Lancarr8/KapTesterV2/Dokumente/Phasen/Extras/Fazit_Selbsteinschaetzung_V2.docx

Fazit und Selbsteinschätzung

KapTester V2 │ Bewertung │ AP2 2026 │ Nico Schmidt

Der folgende Abschnitt bewertet den betrieblichen Auftrag aus persönlicher Sicht: Was wurde erreicht, was lief gut, was hätte besser laufen können und was wurde dabei gelernt.

1 Zielerreichung

Das übergeordnete Ziel – einen funktionsfähigen Kapazitätstester für den Ausbildungsbetrieb zu entwickeln – ist zum Zeitpunkt der Dokumentationsabgabe weitgehend erreicht. Die Hardware-Entwicklung (Schaltplan V2, PCB V2, Bestellung) ist abgeschlossen. Die Platine wurde bestückt, gelötet und in Betrieb genommen. Die Firmware (FW3, kaptesterfw3_v11.hex) ist implementiert und läuft stabil. Ausstehend ist die abschließende Messung mit Referenzkondensatoren.

Ich bin mit dem bisherigen Stand zufrieden. Alle MUSS-Anforderungen des Lastenhefts sind im Design umgesetzt und werden durch die Inbetriebnahme- und Messtests nachgewiesen. Ob das Gerät am Ende vollständig die ±20%-Genauigkeit über den gesamten Bereich einhält, hängt noch vom Firmware-Test ab – das Messprinzip ist jedoch theoretisch und durch die Schaltungsauslegung korrekt.

2 Was gut lief

✓ Motivation und Eigeninitiative

Die Idee, etwas Eigenes zu bauen das tatsächlich im Betrieb eingesetzt werden kann, hat die Motivation über das gesamte Projekt hoch gehalten. Auch wenn die Umsetzung insgesamt mehr Zeit gekostet hat als ursprünglich gedacht, war die Bereitschaft, tiefer einzusteigen, immer vorhanden.

✓ Einstieg in KiCad und PCB-Fertigung

KiCad war zu Projektbeginn noch völlig neu. Der Weg vom ersten Symbol bis zur bestellbaren Gerber-Datei wurde komplett selbst erarbeitet. Ebenso der gesamte PCBWay-Bestellprozess mit Dimensionen, Schichtzahl, Oberflächenbehandlung und Gerber-Kontrolle. Das ist ein Werkzeug, das ich jetzt wirklich kann.

✓ SMD-Löten mit Flux

Vor dem Projekt war ich skeptisch gegenüber SMD-Bauteilen. Mit dem richtigen Flux und einer ordentlichen Lötspitze ist SMD-Löten deutlich einfacher als erwartet – und macht im Vergleich zu THT fast mehr Spaß. Das Ergebnis war optisch und elektrisch besser als gedacht.

3 Größter Fehler und was ich daraus mitgenommen habe

✗ Falsches Schaltplansymbol (DIP-28 statt TQFP-32)

Der teuerste Fehler des Projekts: Das KiCad-Symbol für den ATmega328P-AU war ein DIP-28-Simulations-Symbol ohne korrektes Pin-Mapping. Alle 32 Pins waren falsch verdrahtet. Das wurde erst nach der Bestellung und Lieferung der V1-Platine erkannt – zu spät, um zu stornieren. Die V1-Platine ist nie funktionsfähig gewesen und bleibt als Lernprototyp in der Dokumentation. Die Lektion: Symbol, Footprint und Datenblatt-Pinbelegung müssen vor jeder Bestellung konsequent gegen das Datenblatt geprüft werden – nicht nur stichprobenartig.

4 Was ich gelernt habe

Technisch:

· KiCad vollständig: Schaltplan → Footprint-Zuweisung → PCB-Layout → DRC → Gerber-Export

· PCBWay-Bestellprozess: Gerber-Viewer, Parameter (2L, 1,6mm, TG150, HASL, 1oz)

· SMD-Löten mit Flux – deutlich zugänglicher als gedacht

· LM317 als Konstantstromquelle: I = 1,25V / R – einfach, präzise, robust

· MOSFET-Schaltungen verstehen: PMOS high-side (Verpolschutz), NMOS low-side (Entladepfad)

· ADC-Timing und interne Referenz des ATmega328P

Persönlich / methodisch:

· Footprints und Symbole IMMER gegen Datenblatt prüfen, bevor bestellt wird – nicht nach dem Bestellen

· Mehr Vorab-Nachdenken spart hinten doppelte Arbeit

· Zeitschätzungen bei Hardware-Projekten deutlich großzügiger ansetzen als bei reiner Software

· Dokumentation parallel führen ist besser als alles am Ende nachzuholen

5 Was ich beim nächsten Mal anders machen würde

Footprints früher und genauer prüfen: Jedes neue Symbol sofort mit Datenblatt abgleichen – Pinbezeichnung, Gehäuseform, Pad-Anordnung. Das ist der Schritt, der mich in V1 eine komplette Platine gekostet hat.

Mehr Vorab-Nachdenken: Bevor der Schaltplan im PCB-Editor landet, würde ich mir mehr Zeit nehmen, den Stromfluss und die Schutzschaltungen auf Papier durchzudenken. R20 (Entlade-Schutzwiderstand) und die VGS-Optimierung bei Q1 hätten eigentlich schon in V1 drin sein sollen – sie kamen erst durch Review in V2.

Prototyp zuerst auf Steckbrett: Für die Kernschaltung (LM317 + ATmega + ADC) wäre ein Steckbrett-Test vor dem PCB-Design sinnvoll gewesen, um das Messprinzip real zu validieren.

6 Verbesserungspotenzial am Gerät

Das Gerät funktioniert als Prototyp. Für eine nächste Version oder einen Produktionsstand wären folgende Erweiterungen sinnvoll:

· Gehäuse: Als nackte Platine ist das Gerät anfällig für mechanische Beschädigungen und nicht ESD-geschützt. Ein einfaches 3D-gedrucktes Gehäuse würde das Gerät alltagstauglicher machen.

· Kalibrierung: Aktuell ±20 % ohne Referenznormal. Mit einem bekannten Referenzkondensator und einem Software-Kalibrierungsschritt wäre ±5 % realistisch.

· Polungsunabhängigkeit: Wenn der Kondensator verpolt angeschlossen wird, zeigt das Gerät einen Fehler. Sinnvoller wäre eine automatische Polaritätserkennung und -umschaltung, sodass die Polung des Kondensators egal ist – besonders bei schnellem Werkstatteinsatz praktisch.

· Genauere Messauflösung: Mit einem externen ADC (z.B. 16-Bit ADS1115 via I²C) wäre die Auflösung deutlich besser, besonders für kleine Kapazitäten unter 100 µF.

· ESR-Messung: Eine einfache ESR-Schätzung wäre eine wertvolle Erweiterung – schlechte Elkos haben oft erhöhten ESR lange bevor die Kapazität deutlich abnimmt.

7 Gesamteinschätzung

Das Projekt hat – trotz des Rückschlags mit der V1-Platine – insgesamt Spaß gemacht. Die Kombination aus Schaltungsentwicklung, PCB-Design, Fertigung und Inbetriebnahme ist genau das, was ich mir unter einem betrieblichen Auftrag vorstelle. Das Ergebnis ist kein perfektes Serienprodukt, aber ein funktionsfähiger, dokumentierter Prototyp der zeigt, dass ich den gesamten Weg von der Idee bis zur Inbetriebnahme selbst bestreiten kann.

Alles in allem hat es – auch wenn es manchmal nervig war – wirklich Spaß gemacht.

KapTester V2 · Fazit und Selbsteinschätzung · Nico Schmidt · IHK Osnabrück AP2 2026
