Lancarr8/KapTesterV2/Dokumente/Phasen/Extras/README_Referenz_V2.docx

Persönliche Referenz / README

KapTester V2 │ Nico Schmidt │ AP2 2026

Dieses Dokument ist meine persönliche Zusammenfassung – für die mündliche Prüfung, zum Nachschlagen und als Gedächtnisstütze. Nicht für die IHK-Abgabe bestimmt.

1 Protokoll-Phasen

Phase 0: Planungsanker – Konzept, Lastenheft, Schaltplan, BOM, Risiken

Phase 1: Fertigung – LMP ausfüllen, löten, dokumentieren, Fotos

Phase 2: Sichere Erstinbetriebnahme – spannungsfrei prüfen → kontrolliert einschalten → IBP → übergeben an MP

Phase 3: Nachweis durch Messungen – Messmittel, Messbedingungen, Messpunkte, Ergebnislogik → MP

Phase 4: Formale Abnahme / Freigabe – alle Kriterien geprüft → ANP unterschrieben

2 Schutzklassen (für die mündliche Prüfung)

SK I: Basisisolierung + Schutzleiter (PE) am berührbaren leitfähigen Gehäuse (z. B. Bohrmaschine)

SK II: Doppelte/verstärkte Isolierung, kein PE (z. B. Haartrockner)

SK III: Versorgung ausschließlich über SELV (Schutzkleinspannung, z. B. 12–24 V DC)

KapTester: NA – Baugruppe ohne Gehäuse, SELV 5 V DC → Schutzklasse abhängig von späterer Integration

3 IPC-A-610 Klassen (Lötqualität)

Klasse 1: Consumer / 'funktioniert reicht' – optische Fehler toleriert

Klasse 2: Dedicated Service / solide Industriequalität – langlebig, reproduzierbar (KapTester: Klasse 2)

Klasse 3: High-Reliability / sicherheitskritisch – Luft-/Raumfahrt, Medizintechnik

4 Messprinzip – Kapazitätsformel

Der LM317 erzeugt konstant I = 1,25 V / 1200 Ω = 1,042 mA. Der Kondensator lädt sich linear auf: U(t) = I·t/C. Umgestellt:

C = I × t / U → C = 0,001042 A × t_s / 1,1 V

Bei 100 µF: t = 100×10⁻⁶ × 1,1 / 0,001042 ≈ 0,106 s. Bei 10.000 µF: t ≈ 10,6 s. ATmega stoppt Timer wenn ADC = 1,1 V (interne Referenz).

5 AVR/Firmware – Wichtige Befehle

Fuse Bits setzen (EINMALIG – externer 16-MHz-Quarz):

avrdude -c usbasp -p m328p -U lfuse:w:0xFF:m -U hfuse:w:0xD9:m -U efuse:w:0xFF:m

Firmware flashen:

avrdude -c usbasp -p m328p -U flash:w:kaptester.hex:i

Fuse-Bits lesen (Kontrolle):

avrdude -c usbasp -p m328p -U lfuse:r:-:h -U hfuse:r:-:h

LFUSE 0xFF: Externer Quarz, volle Taktrate (CKSEL=1111, SUT=11)

HFUSE 0xD9: SPIEN=0 (ISP aktiv), EESAVE=1, Bootsize default, keine BOD-Abschaltung

I2C-Adresse: OLED SSD1306 → 0x3C

ADC-Referenz: ADMUX |= (1<<REFS1)|(1<<REFS0) → interne 1,1-V-Referenz

6 V1 → V2 Änderungen (Kerninformation für Prüfung)

Was in V1 falsch war und wie V2 es behebt:

· R6 (Risikoanalyse): ATmega DIP-28-Symbol statt TQFP-32 → alle 32 Pins falsch verdrahtet → V1 nie funktionsfähig

· R7: Kein Serienwiderstand am Q2-Drain → Einschaltstrom bei Großelkos konnte Q2 beschädigen

· Q1 Gate-Teiler: R2 war 100 kΩ → VGS = −2,5 V (suboptimal) → V2: R2 = 1 MΩ → VGS ≈ −4,5 V

· I2C: PC4/PC5 waren no-connect → V2 neu verbunden mit SDA/SCL

7 Testpunkte – Sollwerte Überblick

TP | Netz | Soll | Bedeutung
JTP1 | USB_5V | 4,80–5,20 V | Direkt von USB-VBUS
JTP2 | +5V_BOARD | 4,80–5,20 V | Nach PMOS Q1 – muss ≈ JTP1 sein
JTP4 | LM317_OUT | ≈ 4,5 V (Leerlauf) | LM317 aktiv, kein DUT
JTP5 | GND | 0 V | Massebezug
JTP6 | ADC_MEAS | 0→1,1 V während Messung | Linearer Anstieg
JTP7 | AVCC | ≈ +5V_BOARD | ADC-Versorgung
JTP8 | RESET | ≈ 5 V (Ruhe) | ATmega läuft
JTP9 | MEAS_NODE | 0→1,1 V während Messung | Wie JTP6 aber vor Filter
JTP10 | DISCH_GATE | < 0,1 V (Ruhe) / 5 V (Entladen) | Q2 gesperrt im Ruhezustand

8 Prüflingsdaten (für Abgabe)

Name: Nico Schmidt

Prüflingsnummer: (133)-1251

Ausbildungsberuf: Elektroniker für Geräte und Systeme

Ausbildungsbetrieb: GBS TEMPEST und Service GmbH, Von-Braun-Straße 8, 49356 Diepholz

Projektverantwortlicher: Andreas Moosmann · Tel. 05441 9758100/01 · a.moosmamn@gbs-tempest.de

IHK: IHK Osnabrück – Emsland – Grafschaft Bentheim, Neuer Graben 38, 49074 Osnabrück

Prüfungsdatum: 05.05.2026 (schriftliche Prüfung + Doku-Abgabe)

9 Doku-Checkliste final

✓ Deckblatt (IHK-Formular) → PDF – ausgefüllt und unterschrieben

✓ Erklärung (IHK-Formular) → PDF – ausgefüllt und unterschrieben

✓ Kopie PAO-Antrag → PDF – beigefügt

✓ Kurzbeschreibung IST/SOLL → DOCX – max. 1 Seite – fertig

✓ Dokumentenübersicht Anlagen → DOCX – Seite 2 Kurzbeschreibung – fertig

✓ Kurzbeschreibung der Phasen → DOCX – max. 5 Seiten – fertig

✓ Lastenheft V2 → DOCX – fertig

✓ Blockschaltbild → PNG/PDF – fertig

✓ Technische Schaltungsbeschreibung → DOCX – fertig

✓ Schaltplanauszug V2 (KiCad PDF) → PDF – aus KiCad exportieren

✓ Ablaufplan V2 → DOCX – fertig

✓ BOM V2 → DOCX – fertig

✓ Schnittstellentabelle V2 → DOCX – fertig

✓ Risikoanalyse V2 (R1–R7) → DOCX – fertig

✓ Löt- und Montageprotokoll V2 → DOCX – nach Löten ausfüllen

⏳ Fotos Bestückung V2 → JPG – nach Löten

⏳ Inbetriebnahmeprotokoll V2 → DOCX – nach IBN ausfüllen

⏳ Messprotokoll V2 → DOCX – nach Messung ausfüllen

⏳ Abnahmeprotokoll V2 → DOCX – nach Abnahme ausfüllen

✓ Bedienungsanleitung V2 → DOCX – fertig

✓ Fazit / Selbsteinschätzung → DOCX – nach IBN schreiben

✓ Datenblätter (Anhang) → PDF – ATmega, LM317L, IRLML6402, 2N7002

KapTester V2 · Persönliche Referenz / README · Nico Schmidt · AP2 2026
