Lancarr8/KapTesterV2/Dokumente/Phasen/Information/Lastenheft_V2.docx

Lastenheft

Kapazitätstester – KapTester V2

Dokument | Lastenheft V2.0 – Kapazitätstester | Version: V2.0 │ 26.04.2026
Autor | Nico Schmidt | IHK Osnabrück AP2 2026

1 Ausgangssituation / Problem

Bei Reparatur und Prüfung im Ausbildungsbetrieb müssen Elektrolytkondensatoren schnell auf grobe Kapazitätsabweichungen geprüft werden. Handelsübliche Multimeter sind im Bereich > 1.000 µF ungenau oder zu langsam. Außerdem besteht ein Sicherheitsrisiko durch Restladung und mögliche Verpolung beim Hantieren mit großen Kondensatoren (bis 10.000 µF). Ein dediziertes Prüfmittel ist im Betrieb nicht vorhanden.

2 Ziel des Projekts

Entwicklung eines handlötbaren Kapazitätstesters (Hybrid THT/SMD, 2-lagige Leiterplatte) zur Prüfung von Elektrolytkondensatoren im Bereich 10 µF bis 10.000 µF. Das Gerät soll Verpolschutz, automatischen Entladepfad, Start-Taster und Statusanzeige bieten. Die Messung wird optional auf einem OLED-Display (I²C) und über LEDs angezeigt.

3 Funktionsumfang (MUSS / SOLL / KANN)

Prio | Anforderung (klar, prüfbar) | Akzeptanz / Nachweis
MUSS | Messung Kapazitäten 10 µF – 10.000 µF | Messprotokoll: 5 Referenz-Kondensatoren (10, 100, 1.000, 4.700, 10.000 µF)
MUSS | Verpolung des DUT tolerieren – keine Beschädigung, Fehleranzeige | Test: DUT verpolt → rote LED, keine Erwärmung/Schaden
MUSS | DUT nach Messung automatisch entladen | Test: 4.700 µF laden → nach ≤10 s < 0,1 V (mit DMM gemessen)
MUSS | Messung startet nur nach Start-Taster-Betätigung | Funktionstest
MUSS | Fehlerzustände eindeutig über rote LED anzeigen | Testfälle: verpolt / kein DUT / Timeout
MUSS | Betriebsbereitschaft/OK über grüne LED anzeigen | Funktionstest
MUSS | Messung nach max. 15 s abbrechen und Fehler anzeigen (kein plausibles Ergebnis) | Test: offener Eingang → Timeout + Fehleranzeige
MUSS | Betrieb mit 5 V (USB) Versorgung | Test mit USB-Netzteil
SOLL | Messwert auf OLED-Display in µF anzeigen | OLED-Anzeige (SSD1306, I²C 0x3C)
SOLL | Entladezustand auf OLED anzeigen | OLED-Anzeige während Entladevorgang
KANN | Entladezeit auf OLED anzeigen | Nice-to-have, Firmwareerweiterung

4 Nicht-funktionale Anforderungen (Qualität)

· Handlötbarkeit: THT-Bedienelemente und Stecker, SMD nur TQFP-32 / SOT-23 / SOT-89 / 0805 / MELF

· Service: ISP-Header J4 (AVR-ISP-6) + Testpunkte JTP1–JTP10 für USB5V, 5VBOARD, SDA, LM317IN, GND, ADC, AVCC, RESET, MEAS, DISCH

· Messwiederholbarkeit: bei gleichem DUT drei Messungen innerhalb ±5 % (relativ)

· Sicherheit: automatischer Entladepfad mit Strombegrenzung (R20 = 470 Ω in Serie mit Q2); DUT-Klemme J3 beschriftet (+ / −)

· Layoutqualität: DRC = 0 Fehler, 0 Warnungen vor Bestellung

5 Randbedingungen (Fixpunkte)

Parameter | Festlegung
Versorgung | 5 V DC, USB Micro-B (J1, Molex 47346-0001)
Messprinzip | Konstantstromladung + ADC-Zeitmessung (ATmega328P-AU, intern 1,1-V-Referenz)
Konstantstrom | LM317L (SOT-89) + R8 (1,2 kΩ) → I = 1,25 V / 1.200 Ω = 1,042 mA
Verpolschutz | IRLML6402 PMOS (Q1), Gate-Teiler R2 = 1 MΩ / R3 = 100 kΩ → VGS ≈ −4,5 V
Entladepfad | 2N7002 NMOS (Q2) + R20 = 470 Ω (Strombegrenzer) + R9 = 100 kΩ (Gate-Pull-Down)
Mikrocontroller | ATmega328P-AU, TQFP-32, externer 16-MHz-Quarz (Y1, HC-49/U)
Display | OLED 0,96" SSD1306, I²C (J2, Adresse 0x3C), Pull-Ups R4/R5 = 4,7 kΩ
Fertigung | PCBWay, 2 Layer, FR-4 TG150, 1,6 mm, 1 oz Cu, HASL with lead
Platinenmaß | 90 × 70 mm
Umgebung | Werkstatt / Labor, ESD-Matte, Handhabung unter ESD-Schutz

6 Schnittstellen / Anschlüsse

Ref. | Typ / Footprint | Netz / Pins | Funktion | Bemerkung
J1 | USB Micro-B (Molex 47346-0001) | VBUS, GND | Versorgungseingang 5 V | D+/D− no-connect
J2 | PinHeader 1×4, P2.54 | GND, VCC, SCL, SDA | OLED-Anschluss (I²C) | SSD1306, Adresse 0x3C
J3 | Schraubklemme P5.08, 2-polig | MEAS_NODE (Pin1), GND (Pin2) | DUT-Kondensator | Polung am Silkscreen
J4 | AVR-ISP-6 (2×3, P2.54) | MOSI/MISO/SCK/RESET/VCC/GND | ISP-Programmierung | USBasp, Pin1 markiert
JTP1–10 | PinHeader 1×1, P2.54 | USB5V, 5VBOARD, SDA, LM317IN, GND, ADC, AVCC, RESET, MEAS, DISCH | Testpunkte Inbetriebnahme | Alle wichtigen Netze zugänglich

7 Abnahmekriterien (Definition 'fertig')

Nr. | Testfall | Soll (±20 %) | Ist | OK?
1 | Messung 100 µF Referenzkondensator | 80 µF – 120 µF
2 | Messung 1.000 µF Referenzkondensator | 800 µF – 1.200 µF
3 | Messung 4.700 µF Referenzkondensator | 3.760 µF – 5.640 µF
4 | Messung 10.000 µF Referenzkondensator | 8.000 µF – 12.000 µF
5 | Verpolschutz-Test (DUT verpolt) | Fehleranzeige, kein Schaden, kein Strom
6 | Entladung 4.700 µF nach Messung | < 0,1 V in ≤ 10 s (DMM gemessen)
7 | Kein DUT angeschlossen | Timeout ≤ 15 s, rote LED, OLED Fehlermeldung
8 | Messwiederholbarkeit (3× gleicher DUT) | 3 Messungen innerhalb ±5 % relativ

Messprinzip: Konstantstromladung ohne kalibriertes Referenznormal. Toleranz ±20 % resultiert aus Bauteilstreuung (R8: ±1 %) und interner 1,1-V-Referenz des ATmega (±10 % lt. Datenblatt).

8 Abgrenzung / Nicht-Ziele

· Keine ESR-Messung (Equivalent Series Resistance) · Keine Leckstrommessung als eigener Messwert

· Kein Gehäuse – Prototyp als nackte Leiterplatte · Keine Kalibrierung mit externem Referenznormal

KapTester V2 · Lastenheft V2.0 · Nico Schmidt · IHK Osnabrück AP2 2026
