Lancarr8/KapTesterV2/Dokumente/Phasen/Information/Technische_Schaltungsbeschreibung_V2.docx

Technische Schaltungsbeschreibung

KapTester V2 │ Nico Schmidt │ IHK Osnabrück AP2 2026

Diese Beschreibung erläutert alle Funktionsblöcke der V2-Platine in der Reihenfolge des Signalpfads von der Stromversorgung bis zur Messwertausgabe. Alle Bauteil-Bezeichnungen beziehen sich auf den aktuellen Schaltplan V2 (KiCad).

1. Stromversorgung – J1 – USB Micro-B

Sobald ein USB-Kabel eingesteckt wird, liegen an VBUS 5 V an. Der USB-Standard liefert bis zu 500 mA – für diese Schaltung mit maximal ~50 mA mehr als ausreichend. Die D+/D−-Datenleitungen sind bewusst nicht angeschlossen (no-connect), da nur die Versorgung benötigt wird.

2. Verpolschutz – Q1 (IRLML6402, PMOS) + R2 (1 MΩ) + R3 (100 kΩ)

Die 5 V von USB gelangen zuerst durch Q1, einen P-Kanal-MOSFET. R2 (1 MΩ, nach +USB_5V) und R3 (100 kΩ, nach GND) bilden einen Spannungsteiler: V_Gate ≈ 0,45 V, damit VGS ≈ −4,55 V. Das schaltet Q1 sicher und vollständig durch. Erst nach Q1 entsteht das interne Netz +5V_BOARD, das alle weiteren Stufen speist. Bei Verpolung oder Überspannung bleibt Q1 gesperrt und schützt die gesamte Schaltung.

Hinweis V2: V2-Änderung: R2 wurde von 100 kΩ auf 1 MΩ geändert. Damit liegt VGS bei ca. −4,5 V statt −2,5 V → robusteres Einschalten des PMOS.

3. Statusanzeige – D1 (LED grün, LED_PWR) + R6 (330 Ω) · D2 (LED rot, LED_ERR) + R7 (330 Ω)

Sobald +5V_BOARD anliegt, kann D1 (grüne LED) leuchten. R6 begrenzt den Strom: (5 V − 2 V) / 330 Ω ≈ 9 mA – gut sichtbar, nicht überlastet. D2 (rote LED) mit R7 ist identisch aufgebaut, wird jedoch vom ATmega aktiv gesteuert, z. B. bei Timeout oder Überbereich.

4. Start-Taster – SW1 + R10 (10 kΩ Pull-Up)

R10 hält den Pin START_BTN (ATmega PC2) im Ruhezustand über +5V_BOARD auf High-Pegel. Beim Drücken von SW1 wird der Pin auf GND gezogen → Low-Pegel → ATmega startet die Messung. C8 (10 nF) parallel zu SW1 wirkt als Entprellkondensator.

5. Konstantstromquelle – U2 (LM317L, SOT-89) + R8 (1,2 kΩ)

Der LM317 ist das Herzstück der Messtechnik. Zwischen VO (Ausgang) und ADJ (Stelleingang) liegt R8 (1,2 kΩ). Der LM317 hält intern immer genau 1,25 V über R8, unabhängig von der Last. Daraus ergibt sich ein konstanter Strom: I = 1,25 V / 1.200 Ω = 1,042 mA. Dieser Strom fließt durch den angeschlossenen Kondensator und lädt ihn linear auf.

6. DUT-Anschluss – J3 (Schraubklemme, 2-polig)

An J3 wird der zu messende Kondensator angeschlossen: Pin 1 = MEAS_NODE (Plus), Pin 2 = GND (Minus). Der 1,042-mA-Konstantstrom aus dem LM317 fließt in den Kondensator und lädt ihn linear auf. Der entscheidende Vorteil gegenüber der RC-Methode: Bei konstantem Strom steigt die Spannung am Kondensator exakt linear mit der Zeit an.

7. Messprinzip und ADC-Formel – U1 (ATmega328P-AU, ADC0/PC0)

Während der Kondensator lädt, steigt MEAS_NODE linear: U(t) = (I × t) / C. Umgestellt: C = I × t / U. Der ATmega misst die Zeit t (mit einem 16-Bit-Timer) bis die Spannung U die interne 1,1-V-Referenz erreicht. Da die interne Referenz stabiler als AVCC ist, ist die Schwelle präzise definiert. Bei 100 µF: t = 100×10⁻⁶ × 1,1 / 0,001042 ≈ 0,106 s – gut messbar.

8. ADC-Eingangsfilter – R1 (1 kΩ) + C8 (10 nF)

R1 (1 kΩ) bildet einen Schutzwiderstand vor dem ADC-Eingang (ESD-Schutz, PC0/ADC0). Ein zusätzlicher Filterkondensator ist nicht bestückt.

9. Mikrocontroller – U1 (ATmega328P-AU, TQFP-32)

Der ATmega ist das Steuergehirn: Er liest SW1 (PC2), steuert D1/D2 (PD2, PD3), gibt das Entladesignal aus (PB1 → DISCH_GATE), misst die Spannung (PC0 = ADC0) und berechnet die Kapazität. Wichtige Konfiguration in der Firmware: ADC-Referenz = interne 1,1 V (ADMUX |= (1<<REFS1)|(1<<REFS0)), Timer im CTC-Modus, ADC-Prescaler = 128 (125 kHz bei 16 MHz).

10. Taktgenerator – Y1 (16 MHz Quarz, HC-49/U) + C6/C7 (22 pF)

Der Quarz Y1 schwingt bei exakt 16 MHz. C6 und C7 (je 22 pF, direkt gegen GND) bilden den Lastkreis. Im PCB-Layout sitzen alle drei Bauteile direkt neben den XTAL-Pins mit kürzest möglichen Leiterbahnen. Die ATmega-Fuse-Bits müssen auf externen Quarz gesetzt sein (LFUSE = 0xFF).

11. Entladepfad – Q2 (2N7002, NMOS) + R20 (470 Ω) + R9 (100 kΩ Gate-Pull-Down)

Nach jeder Messung muss der Kondensator entladen werden. Der ATmega zieht DISCH_GATE (PB1) auf High → Q2 öffnet → Kondensator entlädt sich über R20 und Q2 nach GND. R20 (470 Ω) begrenzt den Einschaltstrom bei großen geladenen Elkos und schützt Q2. R9 (100 kΩ) hält das Gate von Q2 im Ruhezustand sicher auf Low, sodass Q2 auch bei tristatetem ATmega-Pin nicht ungewollt leitet.

Hinweis V2: V2-Änderung: R20 (470 Ω) neu hinzugefügt als Schutzwiderstand in Serie mit Q2-Drain. In V1 fehlte dieser – bei großen Elkos hätte der Entladeimpuls Q2 beschädigen können.

12. Abblockkondensatoren – C1/C2/C5 (je 100 nF, VCC) · C3 (100 nF, VCC) · C4 (100 nF, AVCC)

Fünf Keramikkondensatoren direkt an den Versorgungspins des ATmega unterdrücken Stromspitzen beim Schalten digitaler Ausgänge. C4 (AVCC) ist besonders kritisch: Störungen auf der Analog-Versorgung würden den ADC-Messwert direkt verfälschen.

13. ISP-Programmierschnittstelle – J4 (AVR-ISP-6, 2×3-Header, 2,54 mm)

Über J4 wird die Firmware mit einem USBasp-Programmer (10-Pin→6-Pin-Adapter) in den ATmega geladen. Die sechs Pins: MOSI (Daten rein), MISO (Daten raus), SCK (Takt), RESET (Programmierstart), VCC (+5V), GND.

14. OLED-Anzeige – J2 (4-Pin-Header, 2,54 mm) · R4/R5 (je 4,7 kΩ, I²C Pull-Up)

J2 führt die I²C-Leitungen SDA (PC4) und SCL (PC5) des ATmega heraus. R4 und R5 sind die I²C-Bus-Pull-Up-Widerstände nach +5V_BOARD. Ein SSD1306-OLED (0,96", I²C-Adresse 0x3C) zeigt den gemessenen Kapazitätswert an. Pinbelegung J2: Pin 1 = GND, Pin 2 = VCC, Pin 3 = SCL, Pin 4 = SDA.

Messpfad – Zusammenfassung

USB → Q1 (Verpolschutz) → +5V_BOARD → U2/LM317 (1,042 mA) → J3/DUT-Kondensator lädt linear → ATmega misst Zeit bis 1,1 V am ADC → C = I × t / U → OLED zeigt Ergebnis → Q2 + R20 entladen Kondensator

KapTester V2 · Nico Schmidt · IHK Osnabrück · AP2 2026
