Lancarr8/KapTesterV2/Dokumente/Phasen/Planung/Ablaufplan_V2.docx

Ablaufplan V2

KapTester V2 │ Planung │ AP2 2026

Schritte 1–14: Entwicklung und Fertigung V1/V2. Schritte 15–21: Inbetriebnahme, Test und Abschluss.

Nr. | Schritt | Details / Tätigkeiten | Status | Datum

INFORMATION & PLANUNG
1 | Lastenheft erstellen | · Messbereich & Genauigkeitsziel festlegen · Messmethode definieren · Bedienkonzept, Anschlüsse, Randbedingungen | ✅ Erledigt | März 26
2 | Blockdiagramm + Schnittstellentabelle | · Module definieren (ATmega, OLED, Taster, LEDs, LM317, PMOS, Entladepfad) · Netznamen festlegen (ADC_MEAS, MEAS_NODE, DISCH_GATE …) · Signalpfade dokumentieren | ✅ Erledigt | März 26
3 | Risikoanalyse erstellen | · ADC-Rauschen, Quarzstart, Verpolung, Großelko-Entladung analysieren · Gegenmaßnahmen im Layout und Schaltplan definieren | ✅ Erledigt | März 26
4 | Bauteilauswahl / BOM freeze | · THT/SMD-Mix festlegen · Footprints fixieren (Schraubklemme P5.08, Taster H5mm, LED 5mm) · Bestellung planen | ✅ Erledigt | März 26

SCHALTPLAN & PCB V1
5 | Schaltplan V1 fertigungsreif | · Netlabels vollständig · Testpunkte definiert · Pull-Ups, Filter, Vorwiderstände final · ERC = 0 Fehler | ✅ Erledigt | Apr 26
6 | PCB-Planung (Mechanik + Platzierung) | · Boardgröße 80×60 mm (V1) · Platzierungsstrategie: Digital/Analog/Power · Stecker und Bedienelemente an Rand | ✅ Erledigt | Apr 26
7 | KiCad: Schaltplan + Footprints + Annotieren | · Symbol ATmega: FALSCH – DIP-28 statt TQFP-32 verwendet (V1-Fehler, R6) · Footprints zugewiesen, ERC grob geprüft | ✅ Erledigt | Apr 26
8 | KiCad PCB: Board Outline | · Edge.Cuts, Netclasses,· DRC = 0 Fehler (V1) | ✅ Erledigt | Apr 26
9 | Bauteilplatzierung V1 | · Mechanik/Stecker am Rand, MCU zentral · Quarz direkt an XTAL-Pins · ADC-Filter nahe ADC-Pin | ✅ Erledigt | Apr 26
10 | Routing V1 | · XTAL, ADC_MEAS,· GND-Fläche Bottom | ✅ Erledigt | Apr 26
11 | Copper Pour / GND-Stitching | · Bottom GND-Fläche · GND-Vias an MCU, ADC-Filter, Power-Block | ✅ Erledigt | Apr 26
12 | DRC + Fertigungscheck V1 | · DRC = 0 kritische Fehler · Silkscreen ok, Polarity-Marken ok | ✅ Erledigt | Apr 26
13 | Gerber/Drill exportieren V1 | · Alle Layer, PTH+NPTH-Bohrungen · Gerber-Viewer geprüft | ✅ Erledigt | Apr 26
14 | PCBWay Bestellung V1 | · ZIP hochladen, Preview geprüft · V1 bestellt (DIP-28-Fehler entdeckt nach Bestellung) | ✅ Erledigt | Apr 26

SCHALTPLAN & PCB V2 (Fehlerkorrektur)
V2 | V2 Schaltplan + PCB neu erstellt | · ATmega328P-AU TQFP-32 Symbol korrekt (R6 behoben) · PC4/PC5 mit I²C SDA/SCL verbunden · R2 = 1 MΩ (Gate-Teiler Q1, VGS ≈ −4,5 V) · R20 = 470 Ω neu (Entlade-Schutzwiderstand Q2-Drain) · DRC = 0 Fehler · Gerber exportiert · PCBWay V2 bestellt: 90×70 mm, 5 Stück | ✅ Erledigt | 23.05.26

INBETRIEBNAHME & TEST
15 | Bauteile und Platinen V2 annehmen | · Platinen auf Schäden prüfen, Outline messen · Bauteile gegen BOM abgleichen · Fehlende Teile: R4/R5/R20/OLED bestellen | ✅ Erledigt | 23.05.26
16 | Platine V2 bestücken und löten | · Reihenfolge: SMD-Passivteile → SMD-ICs → TQFP-32 → THT → Quarz → USB → Header → Klemme → LEDs/Taster · Lötprotokoll parallel ausfüllen · Fotos: leer / nach SMD / nach THT / Gesamtansicht | ✅ Erledigt | 23.05.26
17 | Abweichungen dokumentieren | · Auffälligkeiten im Lötprotokoll festhalten · Risikoanalyse bei Bedarf aktualisieren | ✅ Erledigt | 23.05.26
18 | Inbetriebnahme V2 | · Kurzschlusscheck (Ohmmeter GND↔+5V) · Ersteinschalten 5 V / 100 mA Strombegrenzung · Spannung JTP1–JTP10 messen · Grüne LED muss leuchten · Inbetriebnahmeprotokoll ausfüllen | ✅ Erledigt | 23.05.26
19 | Firmware flashen (ATmega328P-AU) | · USBasp via J4 (AVR-ISP-6) · Fuse Bits: lfuse 0xFF / hfuse 0xD9 / efuse 0xFF · Firmware kaptester.hex laden · OLED-Anzeige prüfen | ✅ Erledigt | 23.05.26
20 | Funktionsprüfung + Messprotokoll | · 5 Referenz-Kondensatoren: 10 / 100 / 1.000 / 4.700 / 10.000 µF · Verpoltest · Entladetest · Timeout-Test · Ergebnisse in Messprotokoll eintragen | ✅ Erledigt | 23.05.26
21 | Abnahme + Dokumentationsabschluss | · Abnahmeprotokoll ausfüllen · Alle Anlagen zusammenstellen · Fazit / Selbsteinschätzung schreiben · IHK-Deckblatt + Erklärung beifügen | ✅ Erledigt | 23.05.26

KapTester V2 · Ablaufplan V2 · Nico Schmidt · IHK Osnabrück AP2 2026
