Lancarr8/KapTesterV2/Dokumente/Phasen/Planung/Risikoanalyse_V2.docx

Risikoanalyse V2

KapTester V2 │ Planung │ AP2 2026

Identifizierte Risiken, Ursachen, Auswirkungen und umgesetzte Gegenmaßnahmen. Stand V2 (26.04.2026).

ID | Risiko / Status
R1 | ADC-Rauschen / Messwertinstabilität [Im Design berücksichtigt]
| Ursache: Digitale Schaltvorgänge (I²C, ISP, LEDs), Stromsprünge im Lade-/Entladepfad. Auswirkung: Kapazitätswert schwankt, Fehlmessung, Fehltrigger an ADC-Schwelle. Maßnahmen: Zonentrennung Digital/Analog/Power. R1 (1 kΩ) als ESD-Schutz direkt am ADC-Pin . GND-Fläche Bottom + Via-Stitching. ADC_MEAS-Leitung kurz, fern von SCK/SCL. Nachweis: Dreifachmessung gleicher DUT: Streuung ≤ ±5 % (relativ). Gemessen im Messprotokoll.
R2 | Quarz startet nicht / instabiler Takt [Im Design berücksichtigt]
| Ursache: Lange XTAL-Leitungen, Störkopplung durch digitale Signale, schlechter GND-Rückweg Cs. Auswirkung: ATmega startet nicht, sporadische Resets, falsches Timing (Messfehler). Maßnahmen: Y1 + C6/C7 so nah wie möglich an XTAL1/XTAL2 platziert. Kurze, symmetrische XTAL-Leitungen. Saubere GND-Anbindung der Lastkondensatoren. Nachweis: MCU startet reproduzierbar nach Power-On. Firmware läuft stabil.
R3 | Verpolung / Fehlbedienung am DUT-Anschluss [Im Design berücksichtigt]
| Ursache: Elko falsch herum angeschlossen, Klemme verwechselt, Restladung am DUT. Auswirkung: Bauteilschaden (DUT/Schaltung), Fehlmessungen, Sicherheitsrisiko (Erwärmung). Maßnahmen: PMOS Verpolschutz Q1. Eindeutige Silkscreen-Beschriftung DUT+/DUT−. Firmware sperrt Messung bei Unplausibilität und zeigt LED_ERR. Nachweis: Verpolt anschließen: keine Beschädigung, keine Erwärmung, Fehleranzeige aktiv.
R4 | Große Elkos: hohe Energie / Entladung zu langsam / thermische Belastung
| Ursache: Kapazitäten bis 10.000 µF, hohe gespeicherte Energie, zu kleiner Entladepfad. Auswirkung: Lange Wartezeiten, gefährliche Restladung, Bauteilbelastung an Q2. Maßnahmen: Q2 (2N7002) + R20 (470 Ω, V2-neu) als strombegrenzter Entladepfad. R9 = 100 kΩ als Gate-Pull-Down. Firmware überwacht Entladezeit mit Timeout. Nachweis: 4.700 µF nach Messung < 0,1 V in ≤ 10 s. Mit DMM gemessen (Messprotokoll).
R5 | USB-Versorgung instabil / Spannungseinbruch bei Lastwechsel [Im Design berücksichtigt]
| Ursache: Schwaches USB-Netzteil, Stromspitzen beim Laden/Entladen, dünne 5V-Leiterbahn. Auswirkung: Reset, Fehlmessung, sporadisches Verhalten des ATmega. Maßnahmen: 5V-Leiterbahn breiter geroutet. Abblockkondensatoren C1–C5 nahe MCU-Versorgungspins. Betrieb nur an USB-Netzteilen ≥ 500 mA empfohlen. Nachweis: Betrieb an Laptop-USB und Handy-Netzteil stabil über Testdauer.
R6 | Falsches Schaltplansymbol ATmega V1 (DIP-28 statt TQFP-32) [Behoben]
| Ursache: ATmega328-P (DIP-28 Simulation) statt ATmega328P-AU (TQFP-32) im KiCad-Schaltplan verwendet. Alle Pins inkompatibel. Auswirkung: Alle Versorgungspins, XTAL und Signale falsch verdrahtet. V1-Platine nie funktional. Maßnahmen: Symbol in V2 durch ATmega328P-AU (TQFP-32, 32 Pins) ersetzt. Alles neu. Nachweis: V2-Schaltplan per Datenblatt verifiziert. PCB DRC = 0 Fehler. V2 bestellt.
R7 | Fehlender Entladewiderstand Q2 in V1 (Einschaltstrom-Risiko) [Behoben]
| Ursache: In V1 war kein Serienwiderstand am Drain von Q2. Bei vollem 10.000-µF-Elko: fließen kurzzeitig mehrere Ampere durch Q2 Auswirkung: Thermische Überlastung / Zerstörung Q2 bei großen Kondensatoren. Maßnahmen: R20 = 470 Ω neu in V2 in Serie mit Q2-Drain eingefügt. Spannungsabfall während Messung: 470 Ω × 1,042 mA = 0,49 mV – vernachlässigbar. Nachweis: Entladetest 4.700 µF: Q2 bleibt kalt, Entladezeit < 10 s.

KapTester V2 · Risikoanalyse V2 · Nico Schmidt · IHK Osnabrück AP2 2026
