Lancarr8/KapTesterV2/Dokumente/Phasen/Planung/Schnittstellentabelle_V2.docx

Schnittstellentabelle V2

KapTester V2 │ Planung │ AP2 2026

1 Externe Schnittstellen (Anschlüsse nach außen)

Ref. | Typ / Footprint | Signal / Netz | Richtung | Funktion / Bemerkung
J1 | USB Micro-B Molex 47346-0001 | USB_5V (VBUS) GND | Eingang | Versorgungseingang 5 V · D+/D− no-connect
J2 | PinHeader 1×4 P2.54 mm | GND · VCC SCL (PC5) · SDA (PC4) | Ausgang | OLED SSD1306 I²C · Adresse 0x3C · Pull-Ups R4/R5 = 4,7 kΩ
J3 | Schraubklemme Phoenix P5.08 2-pol. | MEAS_NODE (Pin1) GND (Pin2) | Eingang | DUT-Kondensator · Polung Silkscreen · Plus oben
J4 | AVR-ISP-6 PinHeader 2×3 P2.54 | MOSI · MISO · SCK RESET · +5V · GND | Eingang | ISP-Programmierung · USBasp · Pin 1 markiert
SW1 | Taster 6×6 mm H5 mm | START_BTN (PC2) | Eingang | Messung starten · R10 = 10 kΩ Pull-Up · C8 = 10 nF Entpreller
D1 | LED 5 mm grün | LED_PWR (PD2) | Ausgang | Betriebsbereitschaft / OK · R7 = 330 Ω
D2 | LED 5 mm rot | LED_ERR (PD3) | Ausgang | Fehlerzustand · Timeout · Verpolung · R6 = 330 Ω

2 Interne Signale (zwischen Modulen)

Netz / Signal | Von | Zu | Funktion
+5V_BOARD | Q1 (Drain) | Alle Module | Interne 5-V-Versorgung nach Verpolschutz
MEAS_NODE | LM317 (ADJ) / J3-Pin1 | R1, Q2-Drain (über R20) | Messknoten · Ladepunkt · Entladepunkt
LM317_OUT | LM317 (VO) | R8-Pin1 | Konstantstrom-Ausgang vor Setwiderstand
ADC_MEAS | R1-Pin2 | ATmega PC0 (ADC0) | Gefiltertes Messsignal · R1 ESD-Schutz · 1 kΩ · 16 kHz
DISCH_GATE | ATmega PB1 | Q2-Gate / R9 | Entlade-Steuerung · R9 = 100 kΩ Pull-Down
I2C_SDA | ATmega PC4 | J2-Pin4 / R4 | I²C Daten · Pull-Up 4,7 kΩ nach +5V_BOARD
I2C_SCL | ATmega PC5 | J2-Pin3 / R5 | I²C Takt · Pull-Up 4,7 kΩ nach +5V_BOARD
XTAL1/XTAL2 | Y1 + C6/C7 | ATmega PB6/PB7 | 16 MHz Takt · Lastkondensatoren je 22 pF
AVCC | +5V_BOARD | ATmega Pin 18 (AVCC) | Analoge Versorgung ADC · C4 = 100 nF
USB_5V | J1 VBUS | Q1-Source | 5 V vor Verpolschutz
Net-(Q1-G) | R2/R3-Teiler | Q1-Gate | Gate-Spannung PMOS: V_G ≈ 0,45 V · VGS ≈ −4,55 V

3 Testpunkte JTP1 – JTP10

Ref. | Netz | Messziel / Sollwert
JTP1 | USB_5V | Versorgung vor PMOS · Soll: 4,8 – 5,2 V
JTP2 | +5V_BOARD | Versorgung nach PMOS · Soll: 4,8 – 5,2 V (Δ ≤ 50 mV zu JTP1)
JTP3 | I2C_SDA | I²C Daten · Im Betrieb HIGH, Pull-Up aktiv
JTP4 | LM317_OUT | LM317 Ausgang · Soll: +5V_BOARD minus Dropout ≈ 4,5 V (Leerlauf)
JTP5 | GND | Massebezug · Referenz für alle Messungen
JTP6 | ADC_MEAS | Gefiltertes Messsignal · steigt linear während Ladung · max 1,1 V
JTP7 | AVCC | Analoge Versorgung ADC · Soll: ≈ +5V_BOARD · Rauschen < 20 mV
JTP8 | RESET | ATmega Reset · Ruhezustand HIGH (5 V) · Programmierstart: LOW
JTP9 | MEAS_NODE | Rohes Messsignal vor R1-Filter · steigt identisch ADC_MEAS
JTP10 | DISCH_GATE | Entlade-Gate · Ruhezustand LOW · Entladen: HIGH (5 V)

KapTester V2 · Schnittstellentabelle V2 · Nico Schmidt · IHK Osnabrück AP2 2026
