Lancarr8/KapTesterV2/Präsentation/KapTester V2 Abschlusspräsentation (1).pptx

IHK OSNABRÜCK · AP2 2026

KapTester V2

Prüfmittel für Elektrolytkondensatoren
(10 µF – 10.000 µF)

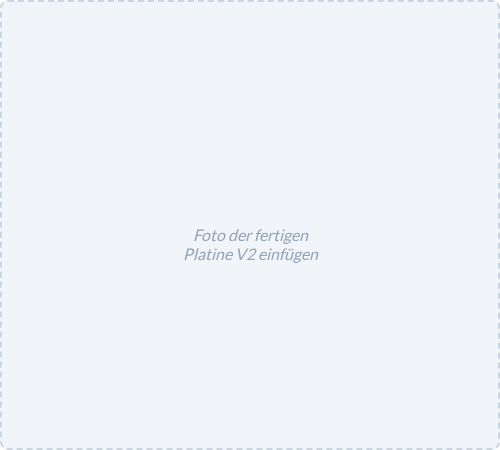
[picture p33: figure]
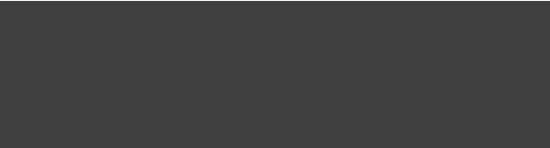
[picture p34: figure]

Nico Schmidt
Elektroniker für Geräte und Systeme

GBS TEMPEST und Service GmbH, Diepholz

KapTester V2 · Nico Schmidt · Prüflingsnr: (133)-1251

## Slide 2

Projekt-Gliederung

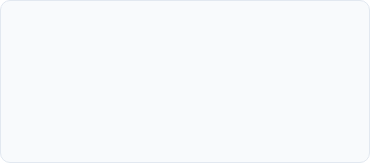
[picture p35: figure]

Analyse der Ausgangslage & präzise Zieldefinition

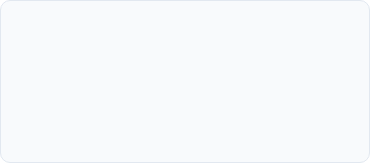
[picture p36: figure]

Physikalische Grundlagen & mathematische Herleitung

Konkretisierung der Systemarchitektur & Bauteile

01 Auftrag

02 Messprinzip

03 Schaltung

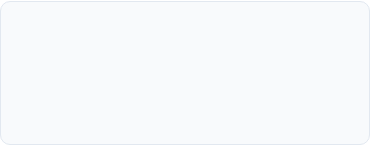
[picture p37: figure]

Analyse des Footprint-Fails & Risiko-Bewertung

Korrekturmaßnahmen & technische Optimierung

Bestückung & Montage nach IPC-A-610 Standard

04 V1 - Fehler

05 V2 - Lösung

06 Fertigung

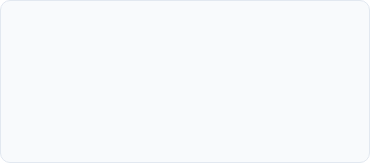
[picture p38: figure]

Effizientes Software-Design in prozessnahem C

Inbetriebnahme-Tests & finales Messprotokoll

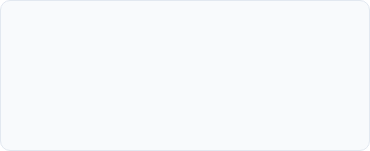
[picture p39: figure]

Zusammenfassung der Learnings & Projektausblick

07 Firmware

08 Validierung

09 Fazit

## Slide 3

Ausgangssituation & Auftrag

✓ Nachweis der Betriebstauglichkeit durch systematisches Messprotokoll.

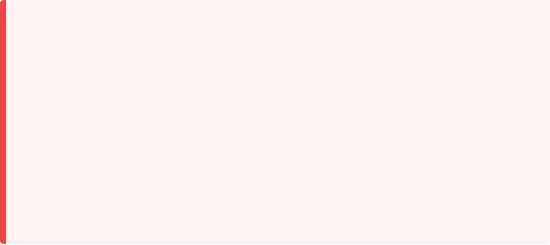
[picture p40: figure]

Das Problem

Kein dediziertes Prüfmittel für große Kapazitäten (> 1 mF) im Werkstattbetrieb verfügbar.

Handelsübliche DMMs ungenau, zu langsam (> 30s) oder begrenzte Messbereiche.

Sicherheitsrisiko durch Restladung/Verpolung bei Elkos.

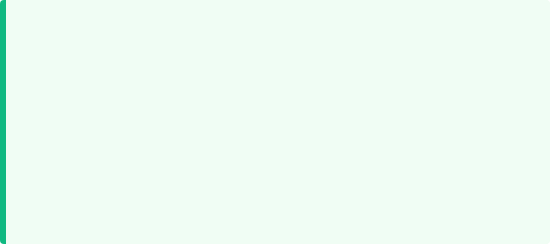
[picture p41: figure]

Das Ziel

Präziser Bereich: 10 µF – 10.000 µF (10 mF).

Integrierter Verpolschutz (PMOS Q1).

Automatischer Entladepfad: ≤ 10s via NMOS Q2.

Klares User-Interface via OLED & Status-LEDs.

•

•

•

•

•

•

•

## Slide 4

Idee & Messprinzip

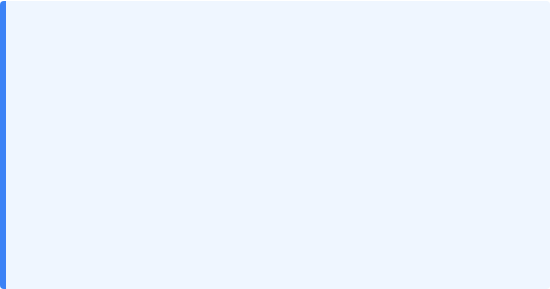
[picture p42: figure]

Messparameter

I = 1,042 mA: Konstantstromquelle via LM317L (1,25V / 1,2kΩ).

ΔU = 1,1 V: Messende bei Erreichen der internen Referenzspannung des ATmega.

t = Ladezeit: Erfasst durch 16-Bit Hardware-Timer Messung.

Das Ergebnis C ist direkt proportional zur gemessenen Zeit t.

Toleranz ±20%: Konservative Angabe inkl. Referenz-Toleranz (±10%), Widerstand (±1%) und Bauteilstreuung. Ermöglicht sichere Gut/Schlecht-Aussage.

## Slide 5

Schaltungsentwurf & System

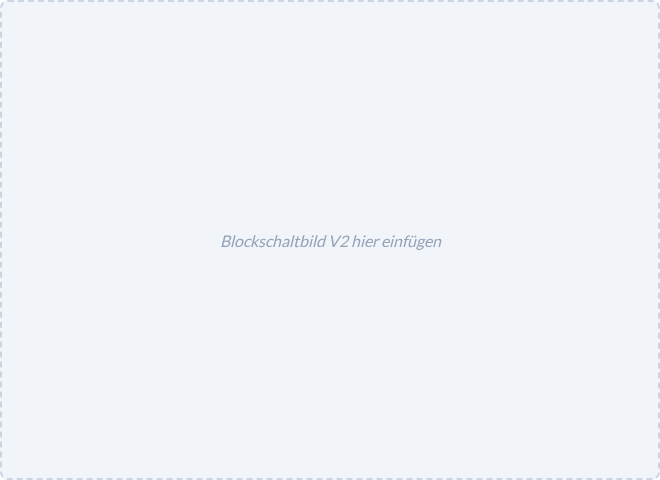
[picture p43: figure]

Schutz & Power

PMOS Verpolschutz; USB 5V Versorgung; Filterung durch Abblockkondensatoren am MCU.

Messpfad

LM317L Stromquelle; NMOS Entladepfad mit 470 Ω Widerstand (Strombegrenzung).

Steuerung

ATmega328P-AU @ 16 MHz Quarz; 10 Testpunkte (JTP1-10) für Wartung/IBN.

## Slide 6

V1 – Kritischer Planungsfehler

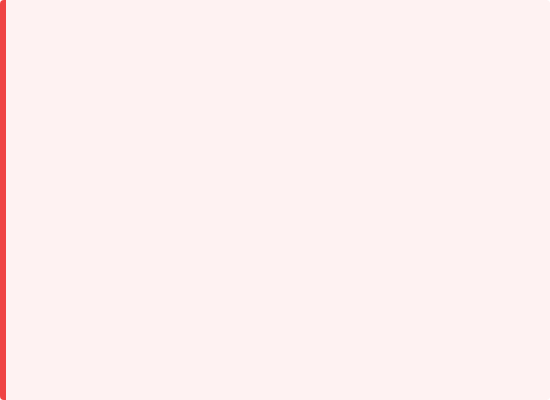
[picture p44: figure]

Analyse Risiko R6

Symbol ≠ Footprint ≠ Real-Bauteil

KiCad-Symbol DIP-28 genutzt, aber physisch TQFP-32 bestellt. Folge: Komplette Fehlverdrahtung der 32 Pins auf dem PCB.

Keine Validierung gegen physikalisches Datenblatt vor PCB-Bestellung.

R20 (Entladewiderstand) fehlte in V1.

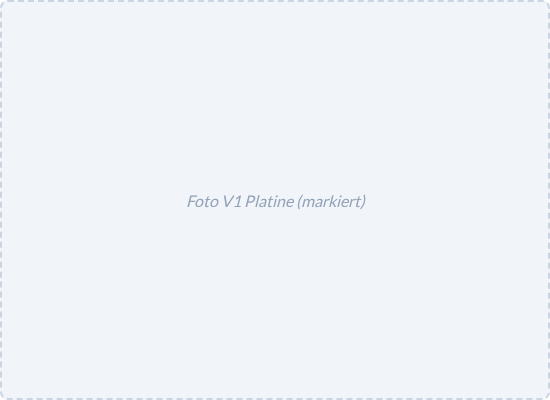
[picture p45: figure]

•

•

## Slide 7

V2 – Systematische Korrekturen

✓ DRC = 0 Fehler · Professionelles Bestückungsdruck-Layout

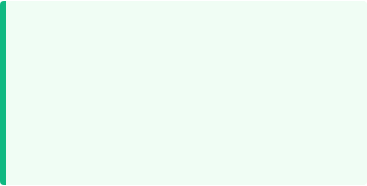
[picture p46: figure]

MCU FIX

Korrektes TQFP-32 Footprint implementiert & komplettes PCB-Routing neu konstruiert.

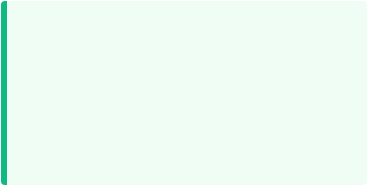
[picture p47: figure]

BAUTEIL-GRUPPIERUNG

Logische Sortierung in Funktionsgruppen (Power, MCU, Messung) zur Störungsminimierung (EMV).

ENTLADE-SCHUTZ

R20 (470 Ω) integriert. Schützt NMOS Q2 vor Entladestromspitzen bei großen Kapazitäten.

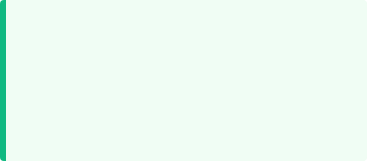
[picture p48: figure]

TESTPUNKTE

Verbesserte JTP-Anordnung für optimale Zugänglichkeit bei Abnahme und Kontrolle.

## Slide 8

Durchführung & Bestückung

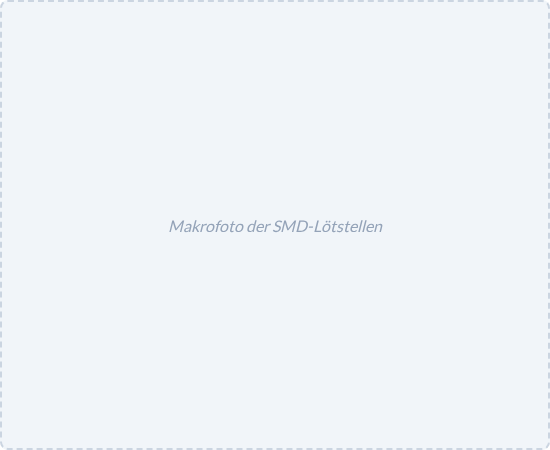
[picture p49: figure]

Fertigungs-Parameter

IPC-A-610 Klasse 2: Abnahme-Standard für industrielle Elektronikfertigung.

SMD-Handlötung: 375 °C Löttemperatur; Fokus auf 0,8 mm Pin-Pitch des TQFP-32.

Bauteilfolge: Passiv (0805) → SMD-ICs → THT-Komponenten (Stecker, LEDs).

QC: Sichtprüfung unter Mikroskop auf Brücken & Kaltlötstellen.

•

•

•

•

## Slide 9

Firmware-Highlights (v3.5)

Kino-Timing:
Flackerfreie UI-Animation, dynamisch angepasst an Ladekurve (220 ms - 450 ms).

2-AUS-3 PLAUSIBILITÄTSFILTER

U_DELTA Kompensation:
Mathematische Korrektur der Restspannung nach Entladung (V2-Fix).

uint32_t

uint32_t

PRÄZISES HARDWARE-POLLING

// Filtert Ausreißer (±15%)

if

if

return

return

do

if

while

break

## Slide 10

Messprotokoll & Validierung

DUT (Nennwert) | Toleranz ±20% | Referenz (DMM) | KapTester V2
10 µF | 8 – 12 µF | [Daten] | [Daten] µF
100 µF | 80 – 120 µF | 104,2 µF | [Daten] µF
1.000 µF | 800 – 1.200 µF | 985,0 µF | [Daten] µF
4.700 µF | 3.760 – 5.640 µF | 4.620,0 µF | [Daten] µF
10.000 µF | 8.000 – 12.000 µF | 9.450,0 µF | [Daten] µF

JTP1-10 Analyse: JTP1: 5,05V (USB); JTP4: 4,45V (LM317); JTP6: 1,1V (ADC); JTP10: 5V (Disch_ON).

Ergebnis: Deterministische Messung & Entladung erfolgreich validiert.

## Slide 11

Fazit & Selbstreflexion

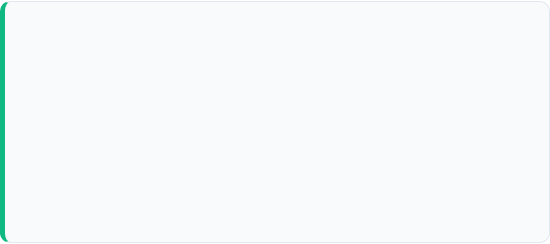
[picture p50: figure]

KiCad: Routing & Footprint-Validierung.

SMD: Bestückung von TQFP-32 & 0805.

Embedded: ATmega Hardware-Timer & ADC.

Coding: C-Systemdesign (Modularität).

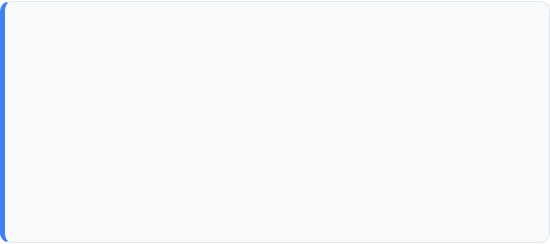
[picture p51: figure]

Prototyping: V1→V2 Iteration als Schlüssel.

Qualität: Firmware-Filterung kompensiert physikalische Toleranzen.

Ausblick: Gehäusebau (3D-Druck) & ESR-Messung Erweiterung.

Reflexion

Learnings

•

•

•

•

•

•

•

## Slide 12

Vielen Dank!

Ich stehe für weitere Fragen bereit!

Nico Schmidt

GBS TEMPEST und Service GmbH, Diepholz

IHK Osnabrück · AP2 2026

## Slide 13

Technisches Datenblatt (Summary)

* Diese Folie dient als visuelle Gedankenstütze während der Q&A Session.

Elektrische Parameter

• Versorgung: 5V USB (± 5%)
• Ladestrom: 1,042 mA (LM317L)
• Ref-Spannung: 1,1 V (intern)

Mess-Spezifikation

• Bereich: 10 µF – 10.000 µF
• Toleranz: ±20% (konservativ)
• Zeitbasis: 16 µs pro Tick

Hardware-Design

• MCU: ATmega328P (16 MHz Quarz)
• Schutz: PMOS IRLML6402
• Entladung: 2N7002 + 470 Ω

Software-Struktur

• 2-aus-3 Plausibilitätsfilter
• Hardware-Polling (Echtzeit)
• Dynamisches Kino-Timing
